fortcollinscreatorhub/rfid-v2/pcb/datasheets-etc/esp32-lcd-114-pinout.webp

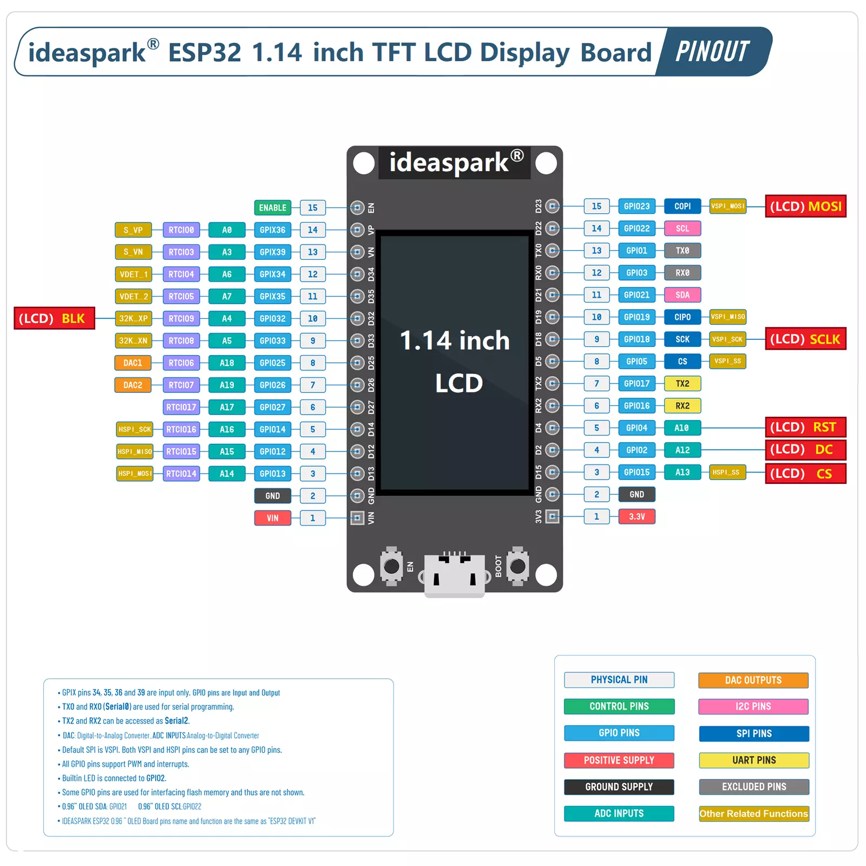
pcb/datasheets-etc/esp32-lcd-114-pinout.webp
