fortcollinscreatorhub/rfid-v2/code/main/app_config.h

// Copyright 2026 Stephen Warren <swarren@wwwdotorg.org>
// SPDX-License-Identifier: MIT

#pragma once

#define ESP_MODULE_IDEASPARK 0
#define ESP_MODULE_LILYGO 1

#define ESP_MODULE ESP_MODULE_LILYGO
